IdeaLabOne/One-3D-Printer/Printed Parts/z axis/z bottom 2x.stl

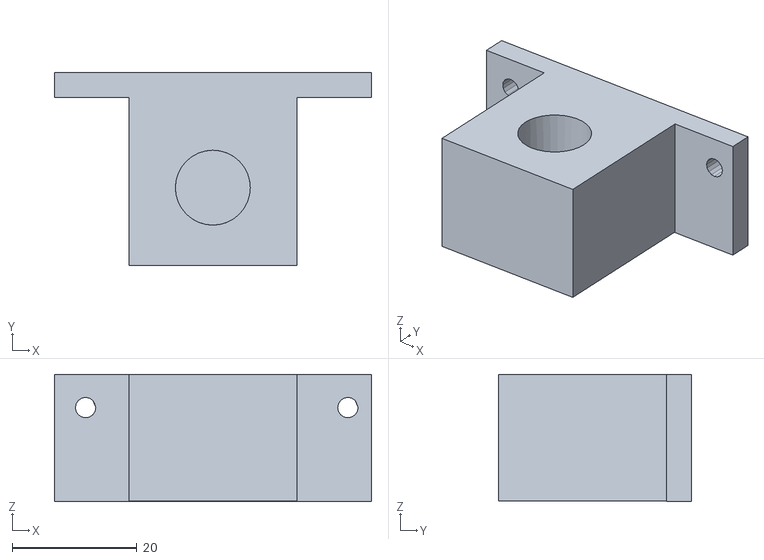
[picture p15: CAD file, 2013-10-23]
Printed Parts/z axis/z bottom 2x.stl
50.8 x 31.0 x 20.4
