IdeaLabOne/One-3D-Printer/Printed Parts/y axis/y smooth rod caps.stl

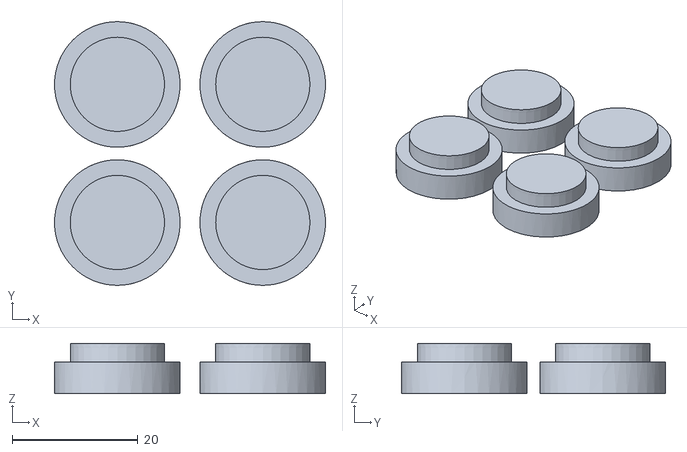
[picture p16: CAD file, 2013-07-19]
Printed Parts/y axis/y smooth rod caps.stl
43.2 x 42.0 x 8.00
