IdeaLabOne/One-3D-Printer/Printed Parts/z axis/top Z.stl

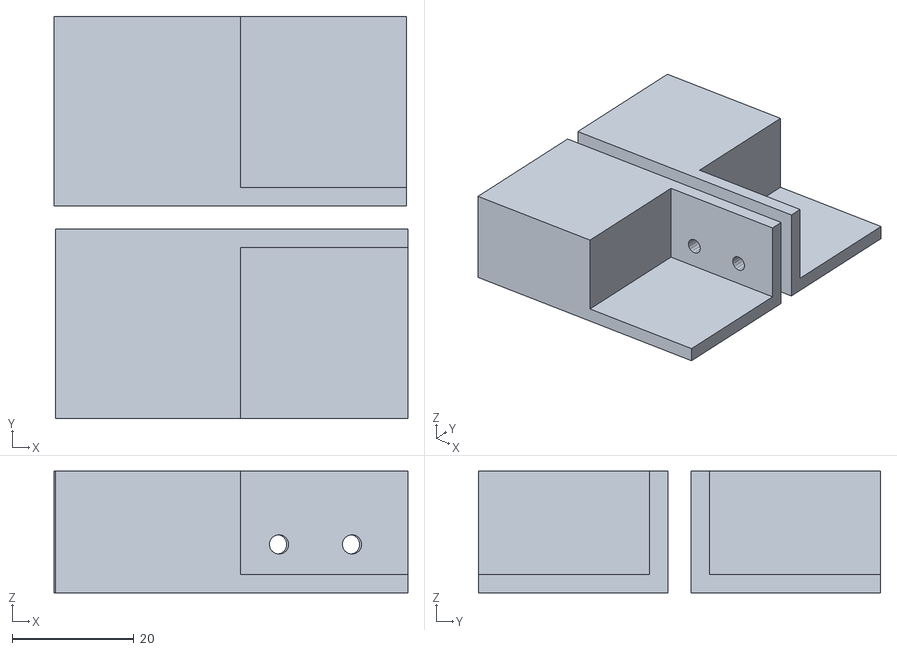
[picture p17: CAD file, 2013-09-05]
Printed Parts/z axis/top Z.stl
58.2 x 66.1 x 20.0
