IdeaLabOne/One-3D-Printer/Printed Parts/z axis/table mount.stl

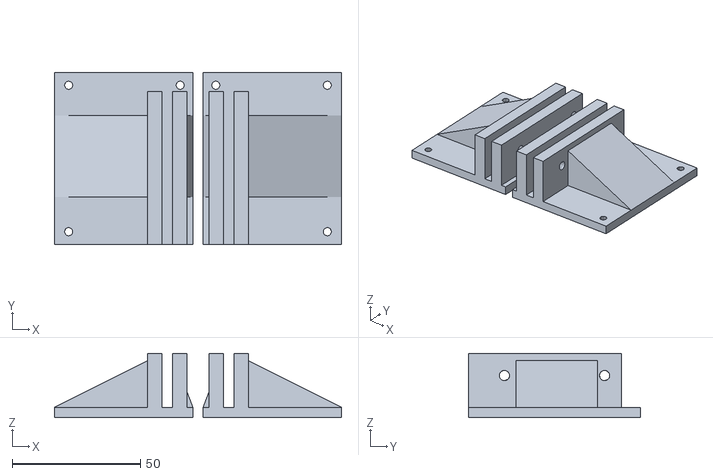
[picture p18: CAD file, 2013-09-05]
Printed Parts/z axis/table mount.stl
111.7 x 67.0 x 25.0
