IdeaLabOne/One-3D-Printer/Printed Parts/z axis/z middle trapez.stl

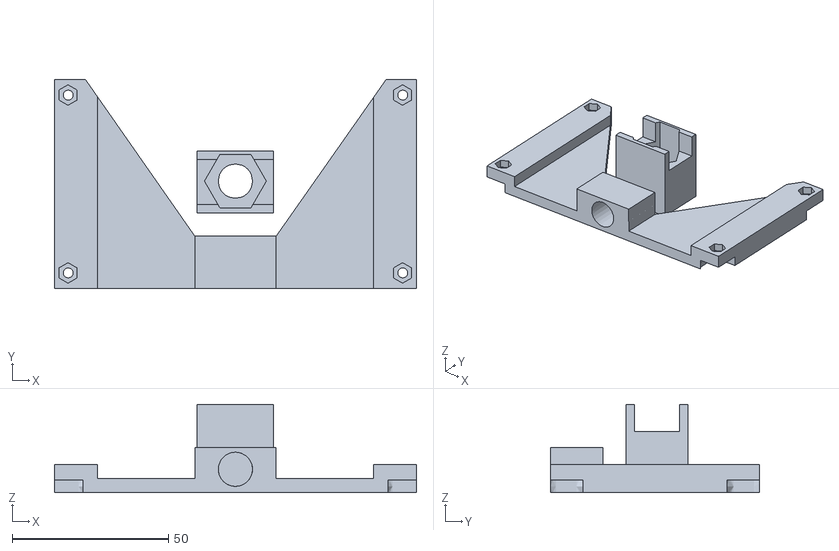
[picture p19: CAD file, 2013-09-05]
Printed Parts/z axis/z middle trapez.stl
116.0 x 67.0 x 28.3
